mck1117/wideband/firmware/wideband_config.h

#pragma once

#include "io_pins.h"
#include "wideband_board_config.h"

// *******************************
//    Defaults
// *******************************
#ifndef EGT_CHANNELS
#define EGT_CHANNELS 0
#endif

// *******************************
//    Nernst voltage & ESR sense
// *******************************

// Heater low pass filter
#define ESR_SENSE_ALPHA (0.002f)

// *******************************
//       Pump current sense
// *******************************

#define PUMP_CURRENT_SENSE_GAIN (10)

// LSU sense resistor - 61.9 ohms
#define LSU_SENSE_R (61.9f)

// Pump low pass filter alpha
// sampling at 2.5khz, alpha of 0.01 gives about 50hz bandwidth
#define PUMP_FILTER_ALPHA (0.02f)

// *******************************
//        Pump controller
// *******************************
#define NERNST_TARGET (0.45f)

#define PUMP_CONTROL_PERIOD 2

// *******************************
//    Heater controller config
// *******************************
#define HEATER_CONTROL_PERIOD 50

#define HEATER_PREHEAT_TIME 5
#define HEATER_WARMUP_TIMEOUT 60

#define HEATER_BATTERY_STAB_TIME 0.5f
// minimal battery voltage to start heating without CAN command
#define HEATER_BATTERY_ON_VOLTAGE 9.5
// mininal battery voltage to continue heating
#define HEATER_BATTERY_OFF_VOLTAGE 7

// *******************************
// Start driving the pump just before we're at target temperature
// minus this offset to avoid Vnerns voltage clamp near 0V
// *******************************
#define START_PUMP_TEMP_OFFSET (200.0)
