mck1117/wideband/for_rusefi/wideband_image.h

static const unsigned char build_wideband_image_bin[] = {
  0x00, 0x05, 0x00, 0x20, 0xa1, 0x19, 0x00, 0x08, 0xb1, 0x4a, 0x00, 0x08,
  0xf9, 0x19, 0x00, 0x08, 0x1d, 0x1a, 0x00, 0x08, 0xf8, 0x19, 0x00, 0x08,
  0x0b, 0x1a, 0x00, 0x08, 0xa3, 0x19, 0x00, 0x08, 0xa3, 0x19, 0x00, 0x08,
  0xa3, 0x19, 0x00, 0x08, 0xa3, 0x19, 0x00, 0x08, 0xa3, 0x19, 0x00, 0x08,
  0xa3, 0x19, 0x00, 0x08, 0xa3, 0x19, 0x00, 0x08, 0xa3, 0x19, 0x00, 0x08,
  0xa3, 0x19, 0x00, 0x08, 0xa3, 0x19, 0x00, 0x08, 0xa3, 0x19, 0x00, 0x08,
  0xa3, 0x19, 0x00, 0x08, 0xa3, 0x19, 0x00, 0x08, 0xa3, 0x19, 0x00, 0x08,
  0xa3, 0x19, 0x00, 0x08, 0xa3, 0x19, 0x00, 0x08, 0xa3, 0x19, 0x00, 0x08,
  0xa3, 0x19, 0x00, 0x08, 0x21, 0x47, 0x00, 0x08, 0xe1, 0x41, 0x00, 0x08,
  0x81, 0x42, 0x00, 0x08, 0x21, 0x43, 0x00, 0x08, 0x81, 0x49, 0x00, 0x08,
  0x11, 0x4a, 0x00, 0x08, 0xb1, 0x47, 0x00, 0x08, 0x21, 0x4a, 0x00, 0x08,
  0xa3, 0x19, 0x00, 0x08, 0xa3, 0x19, 0x00, 0x08, 0xa3, 0x19, 0x00, 0x08,
  0xa3, 0x19, 0x00, 0x08, 0xa3, 0x19, 0x00, 0x08, 0xa3, 0x19, 0x00, 0x08,
  0xa3, 0x19, 0x00, 0x08, 0xa3, 0x19, 0x00, 0x08, 0xa3, 0x19, 0x00, 0x08,
  0xa3, 0x19, 0x00, 0x08, 0xa3, 0x19, 0x00, 0x08, 0xa3, 0x19, 0x00, 0x08,
  0xa3, 0x19, 0x00, 0x08, 0x61, 0x44, 0x00, 0x08, 0xa3, 0x19, 0x00, 0x08,
  0xd1, 0x52, 0x00, 0x08, 0x00, 0x00, 0x00, 0x00, 0x00, 0x00, 0x00, 0x00,
  0x00, 0x00, 0x00, 0x00, 0x72, 0xb6, 0x24, 0x48, 0x80, 0xf3, 0x08, 0x88,
  0x23, 0x48, 0x80, 0xf3, 0x09, 0x88, 0x02, 0x20, 0x80, 0xf3, 0x14, 0x88,
  0xbf, 0xf3, 0x6f, 0x8f, 0x02, 0xf0, 0x2a, 0xfc, 0x03, 0xf0, 0xe8, 0xf8,
  0x1e, 0x48, 0x1f, 0x49, 0x1b, 0x4a, 0x91, 0x42, 0x02, 0xda, 0x08, 0x60,
  0x04, 0x31, 0xfa, 0xe7, 0x1c, 0x49, 0x19, 0x4a, 0x91, 0x42, 0x02, 0xda,
  0x08, 0x60, 0x04, 0x31, 0xfa, 0xe7, 0x1a, 0x49, 0x1a, 0x4a, 0x1b, 0x4b,
  0x9a, 0x42, 0x04, 0xda, 0x08, 0x68, 0x10, 0x60, 0x04, 0x31, 0x04, 0x32,
  0xf8, 0xe7, 0x00, 0x20, 0x17, 0x49, 0x18, 0x4a, 0x91, 0x42, 0x02, 0xda,
  0x08, 0x60, 0x04, 0x31, 0xfa, 0xe7, 0x02, 0xf0, 0x1d, 0xfc, 0x02, 0xf0,
  0x0b, 0xfc, 0x14, 0x4c, 0x14, 0x4d, 0xac, 0x42, 0x03, 0xda, 0x21, 0x68,
  0x88, 0x47, 0x04, 0x34, 0xf9, 0xe7, 0x03, 0xf0, 0x61, 0xf9, 0x11, 0x4c,
  0x11, 0x4d, 0xac, 0x42, 0x03, 0xda, 0x21, 0x68, 0x88, 0x47, 0x04, 0x34,
  0xf9, 0xe7, 0x0f, 0x49, 0x08, 0x47, 0x00, 0x00, 0x00, 0x05, 0x00, 0x20,
  0x00, 0x09, 0x00, 0x20, 0x55, 0x55, 0x55, 0x55, 0x00, 0x01, 0x00, 0x20,
  0x00, 0x05, 0x00, 0x20, 0xa4, 0x68, 0x00, 0x08, 0x00, 0x09, 0x00, 0x20,
  0x14, 0x09, 0x00, 0x20, 0x18, 0x09, 0x00, 0x20, 0xd8, 0x17, 0x00, 0x20,
  0xc0, 0x18, 0x00, 0x08, 0xc4, 0x18, 0x00, 0x08, 0xc4, 0x18, 0x00, 0x08,
  0xc4, 0x18, 0x00, 0x08, 0x61, 0x41, 0x00, 0x08, 0x96, 0xe7, 0x00, 0xf0,
  0x00, 0xf8, 0xfe, 0xe7, 0xf0, 0xb5, 0x44, 0x46, 0x4d, 0x46, 0x56, 0x46,
  0x5f, 0x46, 0xf0, 0xb4, 0x6b, 0x46, 0xcb, 0x60, 0xc3, 0x68, 0x9d, 0x46,
  0xf0, 0xbc, 0xa0, 0x46, 0xa9, 0x46, 0xb2, 0x46, 0xbb, 0x46, 0xf0, 0xbd,
  0x01, 0xf0, 0x92, 0xfe, 0x62, 0xb6, 0x28, 0x1c, 0xa0, 0x47, 0x00, 0x20,
  0x02, 0xf0, 0x94, 0xfb, 0xfe, 0xe7, 0x01, 0xf0, 0xa1, 0xfe, 0x02, 0xf0,
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
};
unsigned int build_wideband_image_bin_len = 25600;
