mck1117/wideband/firmware/boards/f1_dual_rev1/openblt/flash_layout.c

/** \brief   Array wit the layout of the flash memory.
 *  \details Also controls what part of the flash memory is reserved for the bootloader.
 *           If the bootloader size changes, the reserved sectors for the bootloader
 *           might need adjustment to make sure the bootloader doesn't get overwritten.
 */

/* STM32F103RCT6 - high-density device with 256 Kb of flash = 128 pages of 2Kb */
static const tFlashSector flashLayout[] =
{
  /* space is reserved for a bootloader configuration with all supported communication
   * interfaces enabled. when for example only UART is needed, than the space required
   * for the bootloader can be made a lot smaller here.
   */
  /* { 0x08000000, 0x00800 },              flash sector  0 - reserved for bootloader    */
  /* { 0x08000800, 0x00800 },              flash sector  1 - reserved for bootloader    */
  /* { 0x08001000, 0x00800 },              flash sector  2 - reserved for bootloader    */
  /* { 0x08001800, 0x00800 },              flash sector  3 - reserved for bootloader    */
  { 0x08002000, 0x00800 },              /* flash sector  4 - 2kb                        */
  { 0x08002800, 0x00800 },              /* flash sector  5 - 2kb                        */
  { 0x08003000, 0x00800 },              /* flash sector  6 - 2kb                        */
  { 0x08003800, 0x00800 },              /* flash sector  7 - 2kb                        */
#if (BOOT_NVM_SIZE_KB > 16)
  { 0x08004000, 0x00800 },              /* flash sector  8 - 2kb                        */
  { 0x08004800, 0x00800 },              /* flash sector  9 - 2kb                        */
  { 0x08005000, 0x00800 },              /* flash sector 10 - 2kb                        */
  { 0x08005800, 0x00800 },              /* flash sector 11 - 2kb                        */
  { 0x08006000, 0x00800 },              /* flash sector 12 - 2kb                        */
  { 0x08006800, 0x00800 },              /* flash sector 13 - 2kb                        */
  { 0x08007000, 0x00800 },              /* flash sector 14 - 2kb                        */
  { 0x08007800, 0x00800 },              /* flash sector 15 - 2kb                        */
#endif
#if (BOOT_NVM_SIZE_KB > 32)
  { 0x08008000, 0x00800 },              /* flash sector 16 - 2kb                        */
  { 0x08008800, 0x00800 },              /* flash sector 17 - 2kb                        */
  { 0x08009000, 0x00800 },              /* flash sector 18 - 2kb                        */
  { 0x08009800, 0x00800 },              /* flash sector 19 - 2kb                        */
  { 0x0800a000, 0x00800 },              /* flash sector 20 - 2kb                        */
  { 0x0800a800, 0x00800 },              /* flash sector 21 - 2kb                        */
  { 0x0800b000, 0x00800 },              /* flash sector 22 - 2kb                        */
  { 0x0800b800, 0x00800 },              /* flash sector 23 - 2kb                        */
  { 0x0800c000, 0x00800 },              /* flash sector 24 - 2kb                        */
  { 0x0800c800, 0x00800 },              /* flash sector 25 - 2kb                        */
  { 0x0800d000, 0x00800 },              /* flash sector 26 - 2kb                        */
  { 0x0800d800, 0x00800 },              /* flash sector 27 - 2kb                        */
  { 0x0800e000, 0x00800 },              /* flash sector 28 - 2kb                        */
  { 0x0800e800, 0x00800 },              /* flash sector 29 - 2kb                        */
  { 0x0800f000, 0x00800 },              /* flash sector 30 - 2kb                        */
  { 0x0800f800, 0x00800 },              /* flash sector 31 - 2kb                        */
#endif
#if (BOOT_NVM_SIZE_KB > 64)
  { 0x08010000, 0x00800 },              /* flash sector 32 - 2kb                        */
  { 0x08010800, 0x00800 },              /* flash sector 33 - 2kb                        */
  { 0x08011000, 0x00800 },              /* flash sector 34 - 2kb                        */
  { 0x08011800, 0x00800 },              /* flash sector 35 - 2kb                        */
  { 0x08012000, 0x00800 },              /* flash sector 36 - 2kb                        */
  { 0x08012800, 0x00800 },              /* flash sector 37 - 2kb                        */
  { 0x08013000, 0x00800 },              /* flash sector 38 - 2kb                        */
  { 0x08013800, 0x00800 },              /* flash sector 39 - 2kb                        */
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
  { 0x0803a800, 0x00800 },              /* flash sector 117 - 2kb                       */
  { 0x0803b000, 0x00800 },              /* flash sector 118 - 2kb                       */
  { 0x0803b800, 0x00800 },              /* flash sector 119 - 2kb                       */
  { 0x0803c000, 0x00800 },              /* flash sector 120 - 2kb                       */
  { 0x0803c800, 0x00800 },              /* flash sector 121 - 2kb                       */
  { 0x0803d000, 0x00800 },              /* flash sector 122 - 2kb                       */
  { 0x0803d800, 0x00800 },              /* flash sector 123 - 2kb                       */
  { 0x0803e000, 0x00800 },              /* flash sector 124 - 2kb                       */
  { 0x0803e800, 0x00800 },              /* flash sector 125 - 2kb                       */
  { 0x0803f000, 0x00800 },              /* flash sector 126 - 2kb                       */
  { 0x0803f800, 0x00800 },              /* flash sector 127 - 2kb                       */
#endif
#if (BOOT_NVM_SIZE_KB > 256)
#error "BOOT_NVM_SIZE_KB > 256 is currently not supported."
#endif
};


/*********************************** end of flash_layout.c *****************************/
