mck1117/wideband/firmware/boards/f1_common/openblt/led.h

#ifndef LED_H
#define LED_H

/****************************************************************************************
* Function prototypes
****************************************************************************************/
void LedBlinkInit(blt_int16u interval_ms);
void LedBlinkTask(void);
void LedBlinkExit(void);


#endif /* LED_H */
/*********************************** end of led.h **************************************/
